nodang/LineTracer_Gara/스텝 밑판/2021_밑판.SLDPRT

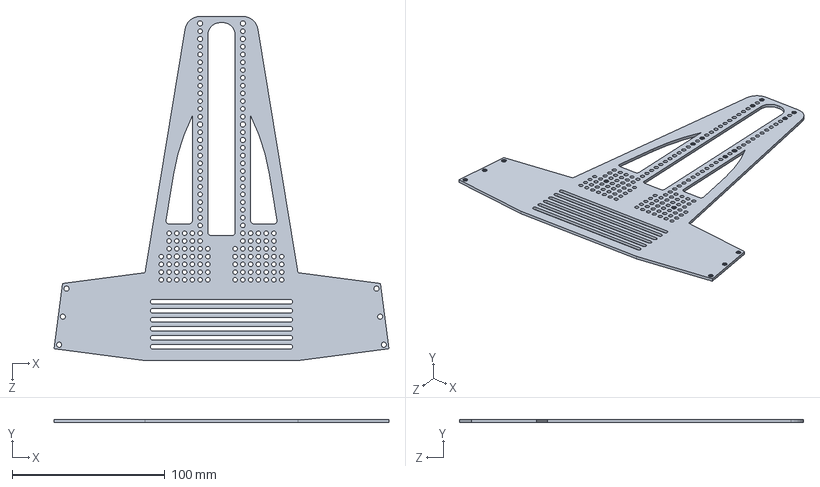
[picture p2: CAD file, 2023-08-02]
스텝 밑판/2021_밑판.SLDPRT
219.0 x 2.00 x 225.0 mm
