nodang/LineTracer_Gara/스텝 밑판/2021_밑판 - 복사본.SLDPRT

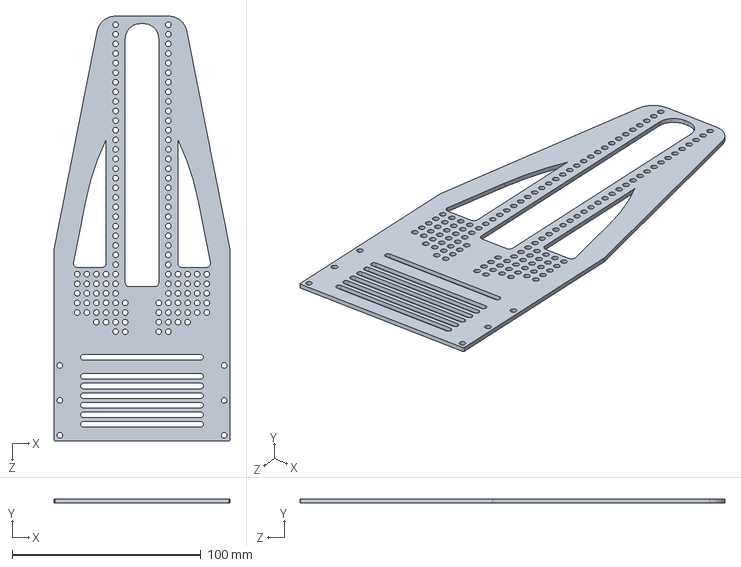
[picture p3: CAD file, 2023-08-02]
스텝 밑판/2021_밑판 - 복사본.SLDPRT
93.0 x 2.00 x 225.0 mm
