nodang/LineTracer_Gara/스텝 밑판/배터리 모형.SLDPRT

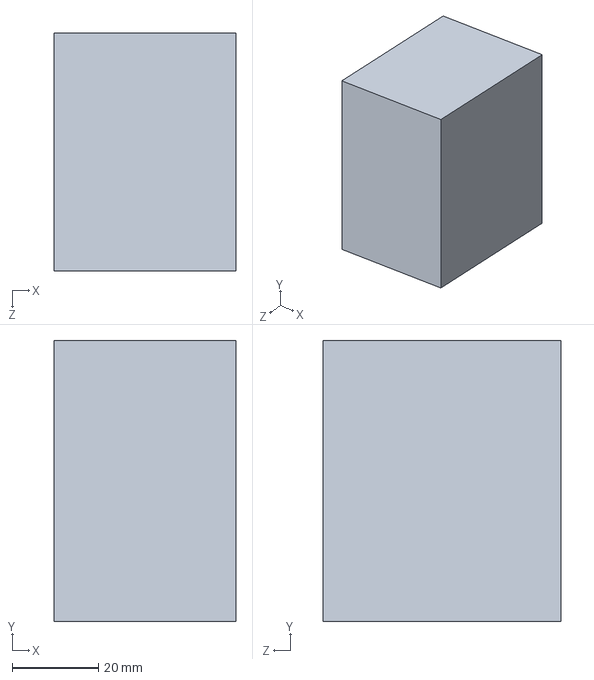
[picture p4: CAD file, 2022-01-03]
스텝 밑판/배터리 모형.SLDPRT
42.0 x 65.0 x 55.0 mm
