nodang/LineTracer_Gara/스텝 밑판/2020_5.STL

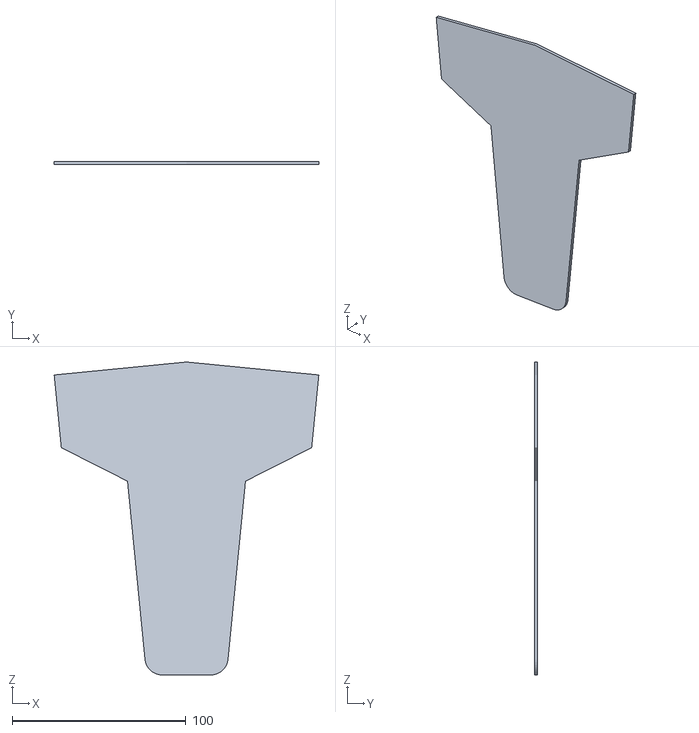
[picture p5: CAD file, 2022-01-03]
스텝 밑판/2020_5.STL
152.2 x 2.00 x 180.0
