nodang/LineTracer_Gara/스텝 밑판/바퀴모형.SLDPRT

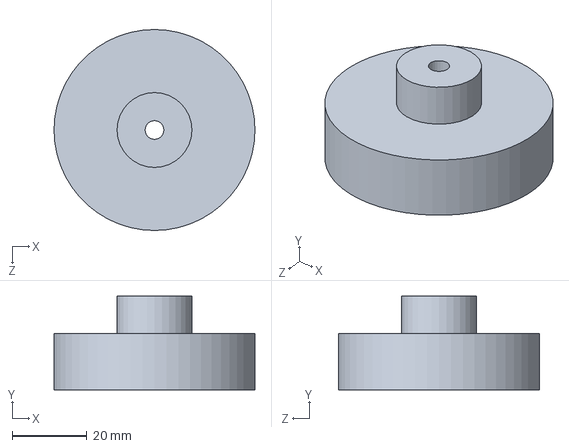
[picture p6: CAD file, 2022-01-03]
스텝 밑판/바퀴모형.SLDPRT
53.7 x 25.0 x 53.7 mm
