nodang/LineTracer_Gara/스텝 밑판/가드.SLDPRT

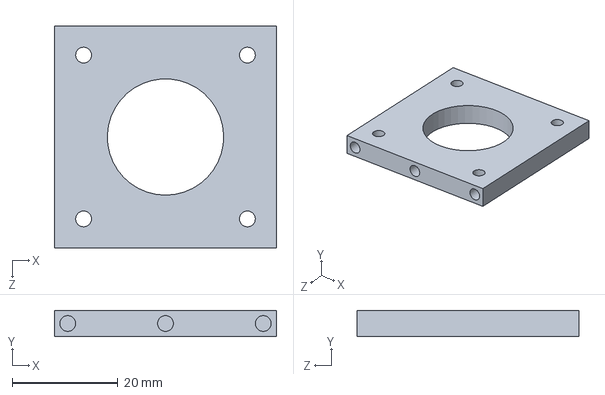
[picture p7: CAD file, 2022-01-03]
스텝 밑판/가드.SLDPRT
42.0 x 5.00 x 42.0 mm
