nodang/LineTracer_Gara/스텝 밑판/KH42JM2-901.SLDPRT

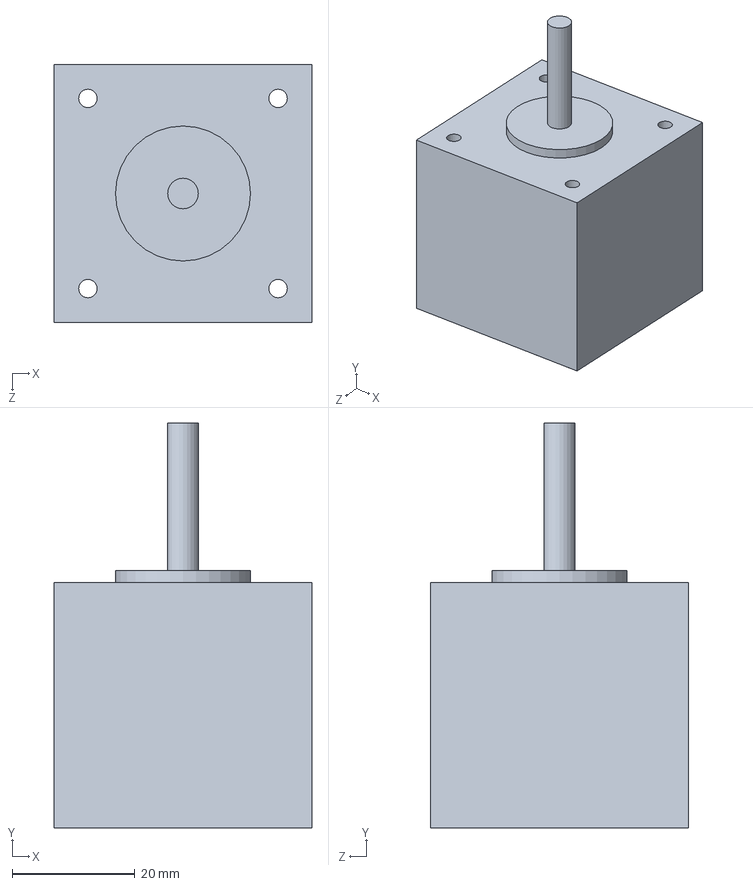
[picture p8: CAD file, 2022-01-03]
스텝 밑판/KH42JM2-901.SLDPRT
42.0 x 66.0 x 42.0 mm
