nodang/LineTracer_Gara/2809_가라_17/main/sensor.h

//###########################################################################
//
// FILE		: senser.h
//
// TITLE	: senser h file
//
// Author	: Yuk Keun Ho
//
// Company	: Maze & Hz
//
//###########################################################################
// $Release Date: 2011.10.10 $
//###########################################################################


#ifndef __SENSOR_H__
#define __SENSOR_H__


#endif

extern void Init_SENSOR();
extern interrupt void SENSOR_ISR();
extern interrupt void ADC_ISR();
extern void SENSOR_MAXMIN();
extern void POSITION_COMPUTE(SENSORADC *pS, int32 *pA, volatile Uint16 *state, volatile Uint16 *enable);
extern void HANDLE();
extern void MARK_ENABLE_SHIFT(TURNMARK *left, TURNMARK *right);
extern void TURN_DECIDE(TURNMARK *mark, TURNMARK *remark);
extern inline void CROSS_CHECK();
