nodang/LineTracer_Gara/2809_가라_17/main/search.c

//###########################################################################
//
// FILE		: search.c
//
// TITLE		: _666_ Tracer search source file.
//
// Author	: Yuk Keun Ho
//
// Company	: Maze & Hertz
//
//###########################################################################
// $Release Date: 2009.11.15 $
//###########################################################################


#include "DSP280x_Device.h"     // DSP280x Headerfile Include File
#include "DSP280x_Examples.h"   // DSP280x Examples Include File

void Init_GLOBAL()
{
 	TIME_INDEX_U32 = 0;
	STOP_TIME_INDEX_U32 = 0;

	MARK_U16_CNT = 0;
	
	SECOND_MARK_U16_CNT = 0;
	
	THIRD_MARK_U16_CNT = 0;
	XRUN_DIST_IQ15 = 0;
	
	ERROR_U16_FLAG = OFF;
	CROSS_PLUS_SEARCH_U32 = 0;
	CROSS_PLUS_U32 = 0;
}

void Init_RUN()
{
	//HandleAccel_IQ17 = _IQ(0.0000333);
	//HandleDecel_IQ17 = _IQ(0.000250);
											// 1500 ABLE								// IDONTKNOW																		//1750 impossible
	//HandleAccel_IQ17 = _IQ(0.0000516);	//HandleAccel_IQ17 = _IQ17(0.00003387);		//HandleAccel_IQ17 = _IQ17(0.00005621);		//HandleAccel_IQ17 = _IQ17(0.00004608);	//HandleAccel_IQ17 = _IQ17(0.00003963);
	//HandleDecel_IQ17 = _IQ17(0.00026249);																							//HandleDecel_IQ17 = _IQ17(0.00080496);	//HandleDecel_IQ17 = _IQ17(0.00060372);
	// weak
	//HandleAccel_IQ17 = _IQ17(0.00002292);		HandleAccel_IQ17 = _IQ17(0.00003441);
	//HandleDecel_IQ17 = _IQ17(0.00013299);		HandleDecel_IQ17 = _IQ17(0.00010213);

	//1700	Acc =  0.000040		Dec = 0.000198
	//		Acc =  0.000017		Dec = 0.000103
	//1800	ACC =  0.000037		Dec = 0.000208
	//1850	Acc =  0.000037		Dec = 0.000258
	//2100	Acc =  0.000040		Dec = 0.000280	
	//2200	Acc =  0.000045		Dec = 0.000290
	//2200	Acc =  0.000041		Dec = 0.000280
	//2300	Acc =  0.000037		Dec = 0.000280
	//2300	Acc =  0.000037		Dec = 0.000278
	//2300	Acc =  0.0000366	Dec = 0.000278

	//2100	Acc =  0.0000300	Dec = 0.000230
	//2350	Acc =  0.0000268	Dec = 0.000285

	//PWM 이후
	//2300	Acc =  0.0000200	Dec = 0.000255		100당 Dec 5 증가 
	//HandleAccel_IQ28 = HandleAcc_IQ28 + _IQ28(((float32)HandleAcc_U16_CNT - 3000.0) * (0.0000001));
	//HandleDecel_IQ28 = HandleDec_IQ28 + _IQ28(((float32)HandleDec_U16_CNT - 2000.0) * (0.000001));

	//sla7052m 이후
	//2000	Acc = 0.0000300		Dec = 0.000700
	//2100	acc = 0.0000247		dec = 0.000590
	//2200	acc = 0.0000293		dec = 0.000582
	//2300	0					570

	//2200	260					250
	//2200	330					205			2차 39.0
	//2100	300					207			2차 40.5

	//new tire
	//2200  150					260
	//2200	200					250			2차 잘안돼이ㅣㅇ
	//2300	50					290			2200은 돼요40.7정도 

	//2300  254					298	 kp = 0.9
	//2400  						 kp = 0.5		0.6 물방울 죽음

	//가라 17
	//2200	285					325	 kp = 1.0		3차 간신히 kp = 0.75에서
	//2100	300					430	 kp = 1.0 		ratio도 1.0에 맞춤 == 21
	//2300 	200					420
	//2200	144					240
	//2100	300					350
	//2300	144					285

	//2300	88					248 3차 맞춤

	//-----------------------------------------------------//
	//	 COEF SAVE
	/*
	SENSOR_SENSITIVE_U16 = 35;

	MOTOR_SPEED_U32 = 2000;
	END_SPEED_U32 = 1900;
	SECOND_MAX_SPEED_U32 = 4000;
	
	x45_SPEED_U32 = 4000;
	xS4S_SPEED_U32 = 2400;
	xS44S_SPEED_U32 = 4000;
	x90_SPEED_U32 = 2200;
	
	JERK_U32 = 8000;
	JERK_LONG_U32 = 20000;
	JERK_MIDDLE_U32 = 25000;
	JERK_SHORT_U32 = 30000;
	
	ACCEL_COEF_I32 = 144; 121
	DECEL_COEF_I32 = 285; 282
	
	D_RATIO_I32 = 24;
	U_RATIO_I32 = 24;
	
	Down_Kp_U32 = 5;
	SHARP_KP_U32 = 30;
	S44S_KP_U32 = 72; 27
	
	PID_Kp_U32 = 100;
	PID_Kd_U32 = 0;
	*/

	Init_SENSOR();
	Init_MOTOR();
	Init_GLOBAL();
	
	memset((void *)&HanPID,0x00,sizeof(HANDLEPID));
	memset((void *)Search,0x00,sizeof(TRACKINFO)*256);

	HanPID.Kp_val_IQ17 = PID_Kp_IQ17;	

	GpioDataRegs.GPACLEAR.all = MOTOR_ResetEnable;

	EPwm1Regs.TBCTL.bit.CLKDIV = EPwm3Regs.TBCTL.bit.CLKDIV = CLK_DIVISION_CONSTANT;	
	EPwm1Regs.TBPRD = EPwm3Regs.TBPRD = (Uint16)MOTOR_PERIOD_MAXIMUM;
}

void RUN(Uint16 number)
{
	const char *table[] = { "        ", "1stREADY", "2ndREADY", "3thREADY", };
		
	Init_RUN();
	
	if(number != 1)	
	{
		load_line_info();
		if(TURN_COMPUTE_FUNC())
		{
			VFDPrintf("cptERROR");
			return;
		}
		
		if(number == 2)
		{
			Flag.Fast_U16 = ON;
			TURN_DIVISION_FUNC();
		}
		else if(number == 3)
		{
			Flag.Extrem_U16 = ON;
			xTURN_DIVISION_FUNC();

			StartCpuTimer2();
		}
		else
			return;
	}
	else 
		Flag.Search_U16 = ON;

	VFDPrintf((char *)table[number]);
	DELAY_US(1000000);
	VFDPrintf("        ");

	GpioDataRegs.GPASET.all = MOTOR_ResetEnable;
	
 	Flag.Sensor_U16 = ON;
	Flag.Motor_U16 = ON;
	
	MOVE_TO_MOVE( _IQ17(500.0), _IQ17(0.0),((long)MOTOR_SPEED_U32) << 17, ((long)MOTOR_SPEED_U32) << 17, ((long)JERK_U32) << 14, MIN_ACC_IQ14 );

	while(1)
	{
#if 0
		//TxPrintf("%6lf,%6lf\n", _IQ17toF(LMotor.NextVelocity_IQ17), _IQ17toF(RMotor.NextAccel_IQ16));
		TxPrintf("%6lf,%6lf\n", _IQ17toF(_IQ17div(STEP_10000D_IQ17, LMotor.PrdNextTranSecon_IQ17)), _IQ17toF(_IQ17div(STEP_10000D_IQ17, RMotor.PrdNextTranSecon_IQ17)));
		//TxPrintf("%6lf,%6lf\n", _IQ17toF(_IQ17div(STEP_10000D_IQ17, LMotor.PrdNextTranSecon_IQ17)), _IQ17toF(_IQ17div(LMotor.FinalVelo_IQ17, LMotor.TargetHandle_IQ17)));
#endif
		//TxPrintf("%lf\n",_IQ17toF(HanPID.Pos_PID_IQ17));
		//TxPrintf("CNT: %u    KP: %lf\n",THIRD_MARK_U16_CNT, _IQ17toF(HanPID.Kp_val_IQ17));
		//TxPrintf("%6ld %d %6ld %d\n", LMotor.PrdNext_IQ14 >> 14, L_PWM.TBCTL.bit.CLKDIV, RMotor.PrdNext_IQ14 >> 14, R_PWM.TBCTL.bit.CLKDIV);
		//TxPrintf("%5.4lf  %5.4lf\n",_IQtoF(LMotor.TargetHandle_IQ17),_IQtoF(RMotor.TargetHandle_IQ17));
#if 0
		TxPrintf("%5ld %5ld %5ld %5ld  %4ld %4ld\n", 
				 LMotor.AccelLimit_IQ14 >> 14, LMotor.NextAccel_IQ14 >> 14, LMotor.NextVelocity_IQ17 >> 17, LMotor.TargetVel_IQ17 >> 17, LMotor.TargetHandle_IQ17 >> 17, RMotor.TargetHandle_IQ17 >> 17);
		//TxPrintf("%lf %lf\n", _IQ17toF(LMotor.NextVelocity_IQ17), _IQ17toF(LMotor.TargetVel_IQ17));
		TxPrintf("%lf %lf %lf %lf\n", _IQ17toF(LMotor.DecelDistance_IQ17), _IQ15toF(LMotor.ErrorDistance_IQ17), _IQ17toF(LMotor.NextVelocity_IQ17), _IQ17toF(LMotor.TargetVel_IQ17));
		//TxPrintf("%lf %lf\n", _IQ17toF(LMotor.DecelDistance_IQ17), _IQ17toF(LMotor.ErrorDistance_IQ17));
#endif

		POSITION_COMPUTE(&SenAdc, POSITION_WEIGHT_I32, &SENSOR_STATE_U16_CNT, &SENSOR_ENABLE);

		LMark.TurnmarkDistance_IQ17 = RMark.TurnmarkDistance_IQ17 = (RMotor.TurnMarkCheckDistance_IQ17 >> 1) + (LMotor.TurnMarkCheckDistance_IQ17 >> 1);
				
		TURN_DECIDE(&RMark, &LMark);
		TURN_DECIDE(&LMark, &RMark);

		XRUN_DIST_IQ15 = (LMotor.GoneDistance_IQ15 >> 1) + (RMotor.GoneDistance_IQ15 >> 1);

		// turnmark err 복구
		if(Flag.Extrem_U16)			err_mark(&THIRD_MARK_U16_CNT);
		else if(Flag.Fast_U16)		err_mark(&SECOND_MARK_U16_CNT);

		if(END_STOP() || LINE_OUT_STOP())		
			return;

		if(ERROR_U16_FLAG)
		{	
			MOVE_TO_MOVE( _IQ17(500.0), _IQ17(0.0),((long)MOTOR_SPEED_U32) << 17, ((long)MOTOR_SPEED_U32) << 17, ((long)JERK_U32) << 14, MIN_ACC_IQ14 );
			ERROR_U16_FLAG = OFF;
		}
	} 
}

void LINE_INFO(TURNMARK *mark)
{
	Search[MARK_U16_CNT].StepCnt_U32 = 0;
	Search[MARK_U16_CNT].Distance_R_U32 = (Uint32)(RMotor.GoneDistance_IQ15 >> 15);
	Search[MARK_U16_CNT].Distance_L_U32 = (Uint32)(LMotor.GoneDistance_IQ15 >> 15);

	LMotor.GoneDistance_IQ15 = RMotor.GoneDistance_IQ15 = _IQ15(0.0);
	
	Search[MARK_U16_CNT].Distance_U32 = (Search[MARK_U16_CNT].Distance_L_U32 + Search[MARK_U16_CNT].Distance_R_U32) >> 1;
	
	if(mark == NULL)
	{
		if(Flag.STOP)	Search[MARK_U16_CNT].TurnWay_U32 = END_LINE;
		else			Search[MARK_U16_CNT].TurnWay_U32 = START_LINE;
	}
	else
	{
		MARK_U16_CNT++;

		Search[MARK_U16_CNT].TurnWay_U32 = (mark == &LMark) ? LEFT_TURN : RIGHT_TURN;
		if(MARK_U16_CNT && Search[MARK_U16_CNT].TurnWay_U32 == Search[MARK_U16_CNT - 1].TurnWay_U32)	Search[MARK_U16_CNT].TurnWay_U32 = STRAIGHT;
	}
}

void LINE_PRINTF()
{
	Uint16	map_U16_cnt = 0;
	Uint16	menu_U16_cnt = 0;
	volatile	Uint16	shutdown_U16 = 1;

	Init_RUN();
	load_line_info();

	VFDPrintf("<-2  3->");
	while(!Flag.Fast_U16 && !Flag.Extrem_U16)
	{
		if(!SW_L)		{	Flag.Fast_U16 = ON;		TxPrintf("\n\nSECOND_LINE_INFO\n\n");		}
		else if(!SW_R)	{	Flag.Extrem_U16 = ON;	TxPrintf("\n\nTHIRD_LINE_INFO\n\n");		}
	}
	DELAY_US(SW_DELAY);

	Flag.TxFlag_U16 = ON;

	TURN_COMPUTE_FUNC();
	
	if(Flag.Extrem_U16)
		xTURN_DIVISION_FUNC();
	else
		TURN_DIVISION_FUNC();

	while(shutdown_U16)
	{
		switch(menu_U16_cnt)
		{
		case 0:
			switch(Search[map_U16_cnt].TurnWay_U32)
			{
			case STRAIGHT:
				VFDPrintf("%3u:S | ",map_U16_cnt);
				break;
			case RIGHT_TURN:
				VFDPrintf("%3u:R |-",map_U16_cnt);
				break;
			case LEFT_TURN:
				VFDPrintf("%3u:L-| ",map_U16_cnt);
				break;
			case START_LINE:
				VFDPrintf("%3u:G-|-",map_U16_cnt);
				break;
			case END_LINE:
				VFDPrintf("%3u:E-|-",map_U16_cnt);
				break;
			default:
				VFDPrintf("%3u: err",map_U16_cnt);
				break;
			}
			break;
		case 1:
			switch(Search[map_U16_cnt].TurnWay_U32)
			{
			case STRAIGHT:
			case RIGHT_TURN:
			case LEFT_TURN:
			case START_LINE:
			case END_LINE:
				VFDPrintf("%3u:%4lu",map_U16_cnt, Search[map_U16_cnt].Distance_U32);
				break;
			default:
				VFDPrintf("%3u: err",map_U16_cnt);
				break;
			}
			break;
		case 2:
			switch(Search[map_U16_cnt].TurnWay_U32)
			{
			case STRAIGHT:
			case RIGHT_TURN:
			case LEFT_TURN:
			case START_LINE:
			case END_LINE:
				VFDPrintf("%3u:%4lx",map_U16_cnt, Search[map_U16_cnt].TurnDir_U32);
				break;
			default:
				VFDPrintf("%3u: err",map_U16_cnt);
				break;
			}
			break;
		}
		if(!SW_U)		{ DELAY_US(SW_DELAY);	shutdown_U16 = 0; }
		else if(!SW_D)	
		{ 
			DELAY_US(SW_DELAY);
			if(menu_U16_cnt < 2)	menu_U16_cnt++;
			else					menu_U16_cnt = 0;
		}
		MENU_SW(&map_U16_cnt, MARK_U16_CNT);
	}
	DELAY_US(SW_DELAY);
}

void time_attack()
{
	Uint16 cnt, turn_cnt;
	Uint32 t, timee[5] = { 0, }, cur = 0;

	//load_line_info();

	turn_cnt = 1;
	while(1)
	{
		VFDPrintf("cnt: %3u", turn_cnt);

		if(!SW_D)
		{
			DELAY_US(SW_DELAY);
			break;
		}
		else if(!SW_R)
		{
			DELAY_US(62500);
			if(turn_cnt > 1)	turn_cnt--;
			else				turn_cnt = 200;
		}
		else if(!SW_L)
		{
			DELAY_US(62500);
			if(turn_cnt < 200)	turn_cnt++;
			else				turn_cnt = 0;
		}
	}

	Init_RUN();

	cnt = 0;
	while(1)
	{
		VFDPrintf("%u|%1lu%1lu%1lu.%1lu%1lu", cnt, timee[4], timee[3], timee[2], timee[1], timee[0]);

		if(!SW_D)
		{
			DELAY_US(SW_DELAY);
			break;
		}
		else if(!SW_U)
		{
			DELAY_US(SW_DELAY);
			if(timee[cnt] > 8)	timee[cnt] = 0;
			else 				timee[cnt]++;
		}
		else if(!SW_R)
		{
			DELAY_US(SW_DELAY);
			if(cnt > 0)			cnt--;
		}
		else if(!SW_L)
		{
			DELAY_US(SW_DELAY);
			if(cnt < 4)			cnt++;
		}
	}

	t = timee[4] * 10000 + timee[3] * 1000 + timee[2] * 100 + timee[1] * 10 + timee[0];
	if(t > 16000)	t = 16000;

	t = t*20;

	DELAY_US(1000000);
	VFDPrintf("        ");

	Flag.Search_U16 = ON;
	
	Flag.Sensor_U16 = ON;
	Flag.Motor_U16 = ON;

	GpioDataRegs.GPASET.all = MOTOR_ResetEnable;
		
	MOVE_TO_MOVE( _IQ17(500.0), _IQ17(0.0),((long)MOTOR_SPEED_U32) << 17, ((long)MOTOR_SPEED_U32) << 17, ((long)JERK_U32) << 14, MIN_ACC_IQ14 );

	while(1)
	{		
		POSITION_COMPUTE(&SenAdc, POSITION_WEIGHT_I32, &SENSOR_STATE_U16_CNT, &SENSOR_ENABLE);

		LMark.TurnmarkDistance_IQ17 = RMark.TurnmarkDistance_IQ17 = (RMotor.TurnMarkCheckDistance_IQ17 >> 1) + (LMotor.TurnMarkCheckDistance_IQ17 >> 1);
	
		TURN_DECIDE(&RMark, &LMark);
		TURN_DECIDE(&LMark, &RMark);

		if(turn_cnt == MARK_U16_CNT)
		{
			MOVE_TO_END(_IQ17(0.0));
			cur = TIME_INDEX_U32;
			
			while(1)
			{
				if(t - 2000 < TIME_INDEX_U32)
				{	
					GpioDataRegs.GPASET.all = MOTOR_ResetEnable;
					Flag.Motor_U16 = ON;
					
					MOVE_TO_MOVE( _IQ17(500.0), _IQ17(0.0),((long)MOTOR_SPEED_U32) << 17, ((long)MOTOR_SPEED_U32) << 17, ((long)JERK_U32) << 14, MIN_ACC_IQ14 );
					
					turn_cnt = 0;
					break;
				}
				else if((RMotor.NextVelocity_IQ17 < MIN_VELO_IQ17) && (RMotor.NextVelocity_IQ17 < MIN_VELO_IQ17))
				{
					Flag.Motor_U16 = OFF;
					EPwm1Regs.CMPA.half.CMPA = EPwm3Regs.CMPA.half.CMPA = 0;

					cur += 1000;
					while(cur > TIME_INDEX_U32);

					GpioDataRegs.GPACLEAR.all = MOTOR_ResetEnable;
				}
				else
					POSITION_COMPUTE(&SenAdc, POSITION_WEIGHT_I32, &SENSOR_STATE_U16_CNT, &SENSOR_ENABLE);
			}
		}
		if(END_STOP() || LINE_OUT_STOP())		
			return;
	} 	
}
