nodang/LineTracer_Gara/2809_가라_17/main/extremerun.h

#ifndef __EXTREMERUN_H__
#define __EXTREMERUN_H__


#endif

extern void LINE_THIRD(TRACKINFO * LINE);
extern void xTURN_DIVISION_FUNC();
extern void xCONTROL(Uint16 mode, HANDLEPID *p_hd, _iq17 ratio, volatile _iq17 kp_min);
extern void err_mark(Uint16 *cnt);
