nodang/LineTracer_Gara/2809_가라_17/main/search.h

//###########################################################################
//
// FILE		: search.c
//
// TITLE		: _varhae_ Tracer search source file.
//
// Author	: leejaeseong
//
// Company	: Hertz
//
//###########################################################################
// $Release Date: 2009.11.15 $
//###########################################################################

#ifndef __SEARCH_H__
#define __SEARCH_H__

extern void Init_GLOBAL();
extern void Init_RUN();
extern void RUN(Uint16 number);
extern void LINE_INFO(TURNMARK * mark);
extern void LINE_PRINTF();
extern void time_attack();

#endif
