nodang/LineTracer_Gara/2809_가라_17/main/Rom.h

//###########################################################################
//
// FILE		: Rom.h
//
// TITLE	: Rom h file.
//
// Author	: Yuk Keun Ho
//
// Company	: Maze & Hz
//
//###########################################################################
// $Release Date: 2011.11.9 $
//###########################################################################

#ifndef __ROM_H__
#define __ROM_H__


#endif


void save_maxmin_rom();
void load_maxmin_rom();
void save_velocity_rom();
void load_velocity_rom();
void save_accel_rom();
void load_accel_rom();
void save_sensitive_rom();
void load_sensitive_rom();
void save_handle_rom();
void load_handle_rom();
void save_pid_rom();
void load_pid_rom();

void save_line_info();
void load_line_info();


/*
void save_value_rom();
void load_value_rom();	
void save_EndAcc_rom();
void load_EndAcc_rom();
*/
