nodang/LineTracer_Gara/2809_가라_17/main/menu.h

//###########################################################################
//
// FILE		: Menu.h
//
// TITLE	: Menu h file.
//
// Author	: Yuk Keun Ho
//
// Company	: MAZE
//
//###########################################################################
// $Release Date: 2011.11.16 $
//###########################################################################

#ifndef __MENU_H__
#define __MENU_H__



#endif

extern Uint16 MENU_SW();
extern Uint16 botMENU_SW();
extern void MENU_PA();
